brrastak/multimeter_module/schematic/multimeter_module.kicad_sch

## KiCad design schematic/multimeter_module.kicad_sch (2025-04-22)

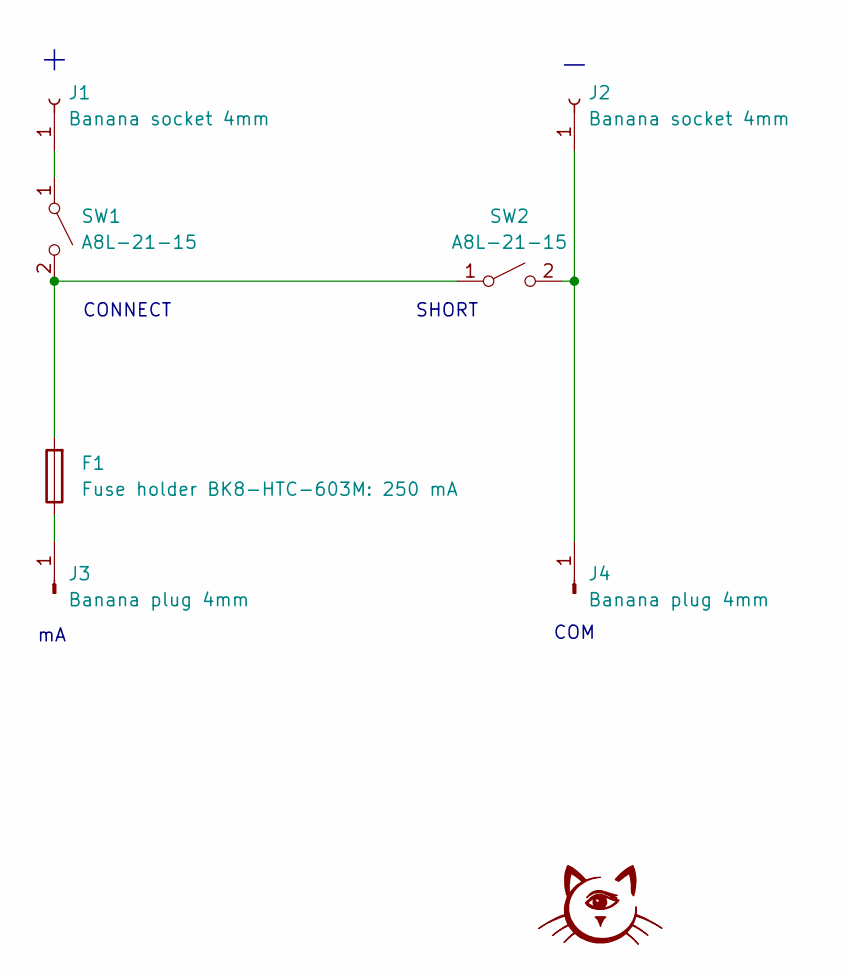
[picture p12: schematic multimeter_module.kicad_sch]

Parts:
F1: Fuse holder BK8-HTC-603M: 250 mA
G1: stamp
J1, J2: Banana socket 4mm
J3, J4: Banana plug 4mm
SW1, SW2: A8L-21-15

Connections:
unnamed: F1.1, J3.1
unnamed: F1.2, SW1.2 (B), SW2.1 (A)
unnamed: J1.1, SW1.1 (A)
unnamed: J2.1, J4.1, SW2.2 (B)

Notes on the sheet:
CONNECT
COM
SHORT
